Tomosawa/MYNOVA-Sparkin/SparkinWin/SparkinClient/Images/main.png

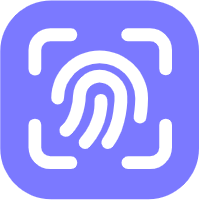
SparkinWin/SparkinClient/Images/main.png
